Board-Folk/PC-Engine-GT-Controller/images/PCEGT-Front-Original-small.png

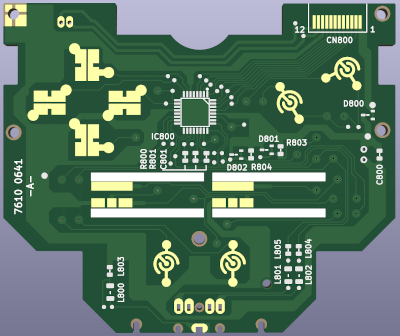
images/PCEGT-Front-Original-small.png
