Board-Folk/PC-Engine-GT-Controller/images/PCEGT-Front-Remaster-small.png

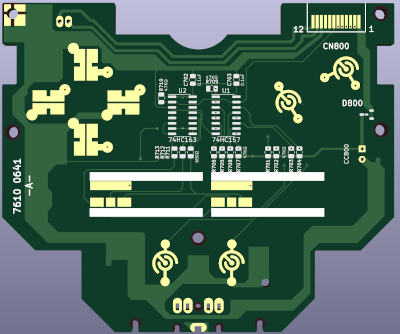
images/PCEGT-Front-Remaster-small.png
